hitomi2500/wasca/fpga_firmware_lattice_module/hdl/top.v

`include "timescale.v"

module top(
    input wire clk_25,
    output wire [5:0] led,
    inout wire sd_cmd,
	inout wire [3:0] sd_dat,
	output wire sd_clk,
    output wire uart_tx,
    input wire uart_rx,
	//A-bus slave interface
	input wire [24:1] abus_address,
	inout wire [15:0] abus_data,
	input wire [2:0] abus_chipselect,
	input wire abus_read,
	input wire [1:0] abus_write,
	output wire abus_interrupt,
	output wire abus_direction,
	output wire abus_interrupt_disable_out,
	output wire abus_buffers_enable,
	//SDRAM port 1 (built into icesugar) master interface
	output wire [12:0] sdram_addr,
	output wire [1:0] sdram_ba,
	output wire sdram_cas_n,
	output wire sdram_cke,
	output wire sdram_cs_n,
	inout wire [15:0] sdram_dq,
	output wire [1:0] sdram_dqm,
	output wire sdram_ras_n,
	output wire sdram_we_n,
	output wire sdram_clk,
	//SDRAM port 2 (external on wasca board) master interface
	output wire [12:0] sdram2_addr,
	output wire [1:0] sdram2_ba,
	output wire sdram2_cas_n,
	output wire sdram2_cke,
	output wire sdram2_cs_n,
	inout wire [7:0] sdram2_dq,
	output wire [1:0] sdram2_dqm,
	output wire sdram2_ras_n,
	output wire sdram2_we_n,
	output wire sdram2_clk,
    //qspi port, unused
    input wire qspi_cs,
    input wire [3:0] qspi_d,
    //i2c
    input wire scsp_clk,
    output wire ssel,
    output wire i2s_bclk,
    output wire i2s_lrclk,
    output wire i2s_dout,
	//debug
	output wire debug_1,
	output wire debug_2,
	output wire debug_3,
	output wire debug_4
);

wire clk_50;
wire clk_133;
wire sd_clk_internal;
wire [3:0] sdram_debug;
wire [0:0] sdram2_dqm_lo;
wire i2s_bclk_internal;
wire i2s_lrclk_internal;
wire i2s_dout_internal;
wire i2s_ssel_internal;
wire i2s_test_enable;

pll_25_133 pll(
    .clk_in_25(clk_25),
    .clk_out_50(clk_50),
    .clk_out_133(clk_133)
);

attosoc soc(
    .mcu_clk_i(clk_50),
    .sdram_clk_i(clk_133),
    .led(led),
    .sd_clk_i(clk_25),
    .sd_cmd(sd_cmd),
    .sd_dat(sd_dat),
    .sd_clk(sd_clk_internal),
    .uart_tx(uart_tx),
    .uart_rx(uart_rx),
    //A-bus slave interface
    .abus_address(abus_address),
    .abus_data(abus_data),
    .abus_chipselect(abus_chipselect),
    .abus_read(abus_read),
    .abus_write(abus_write),
    .abus_interrupt(abus_interrupt),
    .abus_direction(abus_direction),
    .abus_interrupt_disable_out(abus_interrupt_disable_out),
    //SDRAM port 1 (built into icesugar) master interface
    .sdram_addr(sdram_addr),
    .sdram_ba(sdram_ba),
    .sdram_cas_n(sdram_cas_n),
    .sdram_cke(sdram_cke),
    .sdram_cs_n(sdram_cs_n),
    .sdram_dq(sdram_dq),
    .sdram_dqm(sdram_dqm),
    .sdram_ras_n(sdram_ras_n),
    .sdram_we_n(sdram_we_n),
    .sdram_clk(sdram_clk),
    //SDRAM port 2 (external on wasca board) master interface
    .sdram2_addr(sdram2_addr),
    .sdram2_ba(sdram2_ba),
    .sdram2_cas_n(sdram2_cas_n),
    .sdram2_cke(sdram2_cke),
    .sdram2_cs_n(sdram2_cs_n),
    .sdram2_dq(sdram2_dq),
    .sdram2_dqm(sdram2_dqm_lo),
    .sdram2_ras_n(sdram2_ras_n),
    .sdram2_we_n(sdram2_we_n),
    .sdram2_clk(sdram2_clk),
    .sdram_debug(sdram_debug)
);

/*i2s_test_core test_gen(
    .clk(scsp_clk),
    .bck(i2s_bclk_internal),
    .ws(i2s_lrclk_internal),
    .data(i2s_dout_internal),
    .ssel(i2s_ssel_internal)
);*/

assign i2s_test_enable = 0;//sdram_debug[0];

assign ssel = (i2s_test_enable) ? i2s_ssel_internal : 1'b1;//1'b1;//I2S override, should be 1 if not using I2S
assign i2s_bclk = (i2s_test_enable) ? i2s_bclk_internal : 0;
assign i2s_lrclk = (i2s_test_enable) ? i2s_lrclk_internal : 0;
assign i2s_dout = (i2s_test_enable) ? i2s_dout_internal : 0;

assign sd_clk = sd_clk_internal;
assign abus_buffers_enable = 0;//1'b1;
assign sdram2_dqm = {sdram2_dqm_lo[0],sdram2_dqm_lo[0]};
assign debug_1 = 0;//scsp_clk;//abus_address[0];//sdram_debug[0];
assign debug_2 = 0;//i2s_bclk_internal;//abus_address[1];//sdram_debug[1];
assign debug_3 = 0;//i2s_lrclk_internal;//abus_address[2];//sdram_debug[2];
assign debug_4 = 0;//i2s_dout_internal;//abus_address[3];//sdram_debug[3];

endmodule
