hitomi2500/wasca/fpga_firmware_lattice_module/picorv_firmware/firmware.c

#include <stdlib.h>
#include <string.h>
#include <stdint.h>
#include "fatfs/ff.h"
#include "fatfs/sdiodrv.h"
#include "fatfs/diskio.h"
#include "mini-printf.h"

#define VERSION_MAJOR 2
#define VERSION_MINOR 1

#define WISHBONE_REG_PCNTR 0x0
#define WISHBONE_REG_FSCNTRL 0x1
#define WISHBONE_REG_MODE 0x2
#define WISHBONE_REG_HWVER 0x3
#define WISHBONE_REG_SWVER 0x4
#define WISHBONE_REG_SNIFFER_DATA 0x5
#define WISHBONE_REG_SNIFFER_CONTROL 0x8
#define WISHBONE_REG_MAPPER_READ_LO 0x9
#define WISHBONE_REG_MAPPER_READ_HI 0xa
#define WISHBONE_REG_MAPPER_WRITE_LO 0xb
#define WISHBONE_REG_MAPPER_WRITE_HI 0xc
#define WISHBONE_REG_COUNTER_RESET 0xd
#define WISHBONE_REG_RAM_1M_ALIASING 0xe
#define WISHBONE_REG_ID 0xf

#define LED_OFF 0x0
#define LED_EXT_RED 0x20
#define LED_EXT_GREEN 0x10
#define LED_EXT_BLUE 0x8
#define LED_EXT_CYAN (LED_EXT_GREEN | LED_EXT_BLUE)
#define LED_EXT_MAGENTA (LED_EXT_RED | LED_EXT_BLUE)
#define LED_EXT_YELLOW (LED_EXT_RED | LED_EXT_GREEN)
#define LED_EXT_WHITE (LED_EXT_RED | LED_EXT_GREEN | LED_EXT_BLUE)

unsigned char buffer[2048];

#define LED (*(volatile uint32_t*)0x02000000)

#define reg_uart_clkdiv (*(volatile uint32_t*)0x02000004)
//#define reg_uart_data (*(volatile uint32_t*)0x02000008)

#define BLKSIZE 512
#define BLKCNT 10

char roms_filenames[32][64];

__attribute__((aligned(4))) PARTITION VolToPart[FF_VOLUMES] = {
    {0, 0},   // logical drive 0: physical drive 0, auto-detect
};

volatile uint32_t * pWishboneRegs = (uint32_t *)0x01000000;
volatile uint32_t * pSDRAM = (uint32_t *)0x10000000;
volatile uint32_t * pSDRAM2 = (uint32_t *)0x14000000;

__attribute__((aligned(4))) FATFS FatFs;		/* FatFs work area needed for each volume */

int overall_backup_enable = 0;
int overall_backup_counter = 0;

extern void filesystem_access_init();
extern void filesystem_access_scheduler();

void delay() {
    //for (volatile int i = 0; i < 2500000; i++)
    for (volatile int i = 0; i < 750000; i++)
    //for (volatile int i = 0; i < 250; i++)
        ;
}

uint32_t lsfr_next_random (uint32_t prev)
{
	if ( ((prev&0x80000000)/0x80000000)^((prev&0x40000000)/0x40000000)^((prev&0x10)/0x10)^((prev&0x8)/0x8) )
		return  (prev & 0x7FFFFFFF)* 2 + 1;
	else 
		return  (prev & 0x7FFFFFFF)* 2;
}

char* mini_strcpy(char* dest, const char* src) {
    int i = 0;
    while (src[i] != '\0') {
        dest[i] = src[i];
        i++;
    }
    dest[i] = '\0'; // Properly terminate the string
    return dest;
}

char* mini_strcat(char* dest, const char* src) {
    char* ptr = dest;
    while (*ptr != '\0') ptr++; // Find end of dest
    while ((*ptr++ = *src++) != '\0'); // Copy src to dest
    return dest;
}

char* mini_strstr(const char *haystack, const char *needle) {
    // If needle is empty, return the entire haystack
    if (*needle == '\0') return (char *)haystack;

    for (; *haystack != '\0'; haystack++) {
        // If first character matches, check the rest
        if (*haystack == *needle) {
            const char *h = haystack;
            const char *n = needle;
            
            // Compare characters
            while (*h != '\0' && *n != '\0' && *h == *n) {
                h++;
                n++;
            }
            // If we reached the end of the needle, it's a match
            if (*n == '\0') return (char *)haystack;
        }
    }
    return NULL; // Needle not found
}

int sdram_quicktest() {
	volatile uint32_t a;
	int errors = 0;
	uint32_t backup[64];
	//CS0
	backup[0] = pSDRAM[0];
	for (int i=0;i<24;i++)
		backup[i+1] = pSDRAM[1<<i];
	backup[31] = pSDRAM[0xffffff];
	pSDRAM[0] = 0x12345678;
	for (int i=0;i<24;i++)
		pSDRAM[1<<i] = 0x11111111*i;
	pSDRAM[0xffffff] = 0xdeafface;
	a = pSDRAM[0];
	if (a != 0x00005678) {
		mini_printf("SDRAM QUICK error: addr %x write %x read %x\r\n",0,0x00005678,a);
		errors++;
	}
	for (int i=0;i<24;i++) {
		a = pSDRAM[1<<i];
		if (a !=((0x1111*i) & 0xFFFF)) {
			mini_printf("SDRAM QUICK error: addr %x write %x read %x\r\n",1<<i,((0x1111*i) & 0xFFFF),a);
			errors++;
		}
	}
	a = pSDRAM[0xffffff];
	if (a != 0x0000face) {
		mini_printf("SDRAM QUICK error: addr %x write %x read %x\r\n",0xffffff,0x0000face,a);
		errors++;
	}
	pSDRAM[0] = backup[0];
	for (int i=0;i<24;i++)
		pSDRAM[1<<i] = backup[i+1];
	pSDRAM[0xffffff] = backup[31];
	//CS1
	backup[0] = pSDRAM2[0];
	for (int i=0;i<24;i++)
		backup[i+1] = pSDRAM2[1<<i];
	backup[31] = pSDRAM2[0xffffff];
	pSDRAM2[0] = 0x6789;
	for (int i=0;i<23;i++)
		pSDRAM2[1<<i] = 0x1020*i;
	pSDRAM2[0x7fffff] = 0xdeadbeef;
	a = pSDRAM2[0];
	if (a != 0x6789) {
		mini_printf("SDRAM2 QUICK error: addr %x write %x read %x\r\n",0,0x6789,a);
		errors++;
	}
	for (int i=0;i<23;i++) {
		a = pSDRAM2[1<<i];
		if (a !=((0x1020*i) & 0xFFFF)) {
			mini_printf("SDRAM2 QUICK error: addr %x write %x read %x\r\n",1<<i,((0x1020*i) & 0xFFFF),a);
			errors++;
		}
	}
	a = pSDRAM2[0x7fffff];
	if (a != 0xbeef) {
		mini_printf("SDRAM2 QUICK error: addr %x write %x read %x\r\n",0x7fffff,0xbeef,a);
		errors++;
	}
	pSDRAM2[0] = backup[0];
	for (int i=0;i<24;i++)
		pSDRAM2[1<<i] = backup[i+1];
	pSDRAM2[0xffffff] = backup[31];	
	return errors;
}

void backup_sync_sector(int sector, FIL * _file) {
	int written = 0;
	uint16_t * buffer16 = (uint16_t *)buffer;
	//sync data
	for (int i=0;i<256;i++)
		buffer16[i] = pSDRAM2[sector*256+i];
	f_lseek(_file,sector*512);
	int result = f_write(_file,buffer,512,&written);
	if (result)
		mini_printf("Sync error at %d, written %d result %d\r\n",sector,written,result);
	result = f_sync(_file);
	if (result)
		mini_printf("Sync error2 at %d, written %d result %d\r\n",sector,written,result);
}

void sniffer_purge_fifo () {
	volatile int dummy;
	while ((pWishboneRegs[WISHBONE_REG_SNIFFER_CONTROL]>>16) > 100) //purging fifo
		dummy = pWishboneRegs[WISHBONE_REG_SNIFFER_DATA];
}

void prepare_advertisement (int roms_count) {
	FILINFO _filinfo;
	//preparing advertisement lines for modes at the middle of CS0
	volatile uint32_t * pAdvertise = (uint32_t *)0x12000000;
	char adv_string[64];
	uint16_t * adv_string16 = (uint16_t*)adv_string;
	int adv_offset = 0;
	int id = 1;
	//power memory 0.5
	pAdvertise[adv_offset] = (id++)<<8;
	memset(adv_string,0,64);
	if (FR_OK == f_stat("backup05.bin", &_filinfo))
		mini_strcpy(adv_string,"BACKUP 0.5M (backup05.bin)");
	else
		mini_strcpy(adv_string,"BACKUP 0.5M (New file: backup05.bin)");
	for (int i=0; i<31;i++)
		pAdvertise[adv_offset+i+1] = adv_string16[i];
	adv_offset+= 32;
	//power memory 1
	memset(adv_string,0,64);
	pAdvertise[adv_offset] = (id++)<<8;
	if (FR_OK == f_stat("backup1.bin", &_filinfo))
		mini_strcpy(adv_string,"BACKUP 1M (backup1.bin)");
	else
		mini_strcpy(adv_string,"BACKUP 1M (New file: backup1.bin)");
	for (int i=0; i<31;i++)
		pAdvertise[adv_offset+i+1] = adv_string16[i];
	adv_offset+= 32;
	//power memory 2
	memset(adv_string,0,64);
	pAdvertise[adv_offset] = (id++)<<8;
	if (FR_OK == f_stat("backup2.bin", &_filinfo))
		mini_strcpy(adv_string,"BACKUP 2M (backup2.bin)");
	else
		mini_strcpy(adv_string,"BACKUP 2M (New file: backup2.bin)");
	for (int i=0; i<31;i++)
		pAdvertise[adv_offset+i+1] = adv_string16[i];
	adv_offset+= 32;
	//power memory 4
	memset(adv_string,0,64);
	pAdvertise[adv_offset] = (id++)<<8;
	if (FR_OK == f_stat("backup4.bin", &_filinfo))
		mini_strcpy(adv_string,"BACKUP 4M (backup4.bin)");
	else
		mini_strcpy(adv_string,"BACKUP 4M (New file: backup4.bin)");
	for (int i=0; i<31;i++)
		pAdvertise[adv_offset+i+1] = adv_string16[i];
	adv_offset+= 32;
	//1M RAM
	memset(adv_string,0,64);
	pAdvertise[adv_offset] = (id++)<<8;
	mini_strcpy(adv_string,"RAM 1M");
	for (int i=0; i<31;i++)
		pAdvertise[adv_offset+i+1] = adv_string16[i];
	adv_offset+= 32;
	//4M RAM
	memset(adv_string,0,64);
	pAdvertise[adv_offset] = (id++)<<8;
	mini_strcpy(adv_string,"RAM 4M");
	for (int i=0; i<31;i++)
		pAdvertise[adv_offset+i+1] = adv_string16[i];
	adv_offset+= 32;
	//special Heart of Darkness mode
	memset(adv_string,0,64);
	pAdvertise[adv_offset] = (id++)<<8;
	mini_strcpy(adv_string,"RAM (Heart of Darkness)");
	for (int i=0; i<31;i++)
		pAdvertise[adv_offset+i+1] = adv_string16[i];
	adv_offset+= 32;
	//now listing rom files
	for (int i=0;i<roms_count;i++){
		memset(adv_string,0,64);
		pAdvertise[adv_offset] = (id++)<<8;
		mini_strcpy(adv_string,"ROM (");
		mini_strcat(adv_string,roms_filenames[i]);
		mini_strcat(adv_string,")");
		for (int i=0; i<31;i++)
			pAdvertise[adv_offset+i+1] = adv_string16[i];
		adv_offset+= 32;
	}
	pAdvertise[adv_offset] = 0;//end of advertising list
}

void report_readiness (int percent) {
	pWishboneRegs[WISHBONE_REG_PCNTR] = percent;
}

void prepare_mode () {
	FILINFO _filinfo;
	int creating_backup = 0;
	FIL _file;
	unsigned int readen;
	uint16_t * buffer16 = (uint16_t *)buffer;
	int offset;
	//executing prepare sequence
	switch (pWishboneRegs[WISHBONE_REG_MODE]) {
		case 0:
			//some error? we never advertised 0
			pWishboneRegs[WISHBONE_REG_ID] = 0xFFFF;
			report_readiness(100);
			LED = LED_EXT_RED;
			break;
		case 1:
			pWishboneRegs[WISHBONE_REG_ID] = 0xFF21;
			if (FR_OK != f_stat("backup05.bin", &_filinfo))
			{
				creating_backup = 1;
				f_open(&_file,"backup05.bin",FA_CREATE_ALWAYS | FA_WRITE);
				for (int i=0;i<1024*2;i++) {
					backup_sync_sector(i,&_file);
					report_readiness((i * 50)/(1024*2));
					LED = (i&0x40) ? LED_EXT_MAGENTA : LED_OFF;
				}
				f_close(&_file);
			}
			f_open(&_file,"backup05.bin",FA_READ);
			f_lseek(&_file,0);
			for (int i=0;i<1024;i++) {
				f_read(&_file,buffer,1024,&readen);
				for (int j=0;j<512;j++) {
					pSDRAM2[i*512+j] = buffer16[j];
				}
				report_readiness( (creating_backup) ? 50 + (i*50)/1024 : (i*100)/1024 );
				LED = (i&0x20) ? LED_EXT_YELLOW : LED_OFF;
			}
			f_close(&_file);
			//keep file open
			report_readiness(100);
			pWishboneRegs[WISHBONE_REG_MAPPER_READ_LO] = 0xFFFFFFFF;//allow full CS0 RAM in backup more
			pWishboneRegs[WISHBONE_REG_MAPPER_WRITE_LO] = 0xFFFFFFFF;//allow full CS0 RAM in backup more
			pWishboneRegs[WISHBONE_REG_MAPPER_WRITE_HI] = 0x0000FFFF;//enable write for CS1
			LED = LED_EXT_GREEN;
			break;
		case 2:
			pWishboneRegs[WISHBONE_REG_ID] = 0xFF22;
			report_readiness(1);
			if (FR_OK != f_stat("backup1.bin", &_filinfo))
			{
				creating_backup = 1;
				f_open(&_file,"backup1.bin",FA_CREATE_ALWAYS | FA_WRITE);
				for (int i=0;i<2048*2;i++) {
					backup_sync_sector(i,&_file);
					report_readiness( (i * 50)/(2048*2) );
					LED = (i&0x40) ? LED_EXT_MAGENTA : LED_OFF;
				}
				f_close(&_file);
			}
			f_open(&_file,"backup1.bin",FA_READ);
			offset = 0;
			while(false == f_eof(&_file)) {
				readen = -1;
				f_read(&_file,buffer,1024,&readen);
				for (int i=0;i<512;i++) {
					pSDRAM2[offset+i] = buffer16[i];
				}
				offset+=512;
				report_readiness( (creating_backup) ? 50 + offset/20972 : offset/10486 );
				LED = (offset&0x4000) ? LED_EXT_YELLOW : LED_OFF;
			}
			f_close(&_file);
			//keep file open
			report_readiness(100);
			pWishboneRegs[WISHBONE_REG_MAPPER_READ_LO] = 0xFFFFFFFF;//allow full CS0 RAM in backup more
			pWishboneRegs[WISHBONE_REG_MAPPER_WRITE_LO] = 0xFFFFFFFF;//allow full CS0 RAM in backup more
			pWishboneRegs[WISHBONE_REG_MAPPER_WRITE_HI] = 0x0000FFFF;//enable write for CS1
			LED = LED_EXT_GREEN;
			break;
		case 3:
			pWishboneRegs[WISHBONE_REG_ID] = 0xFF23;
			report_readiness(1);
			if (FR_OK != f_stat("backup2.bin", &_filinfo))
			{
				creating_backup = 1;
				f_open(&_file,"backup2.bin",FA_CREATE_ALWAYS | FA_WRITE);
				for (int i=0;i<4096*2;i++) {
					backup_sync_sector(i,&_file);
					report_readiness( (i * 50)/(4096*2) );
					LED = (i&0x40) ? LED_EXT_MAGENTA : LED_OFF;
				}
				f_close(&_file);
			}
			f_open(&_file,"backup2.bin",FA_READ);
			offset = 0;
			while(false == f_eof(&_file)) {
				readen = -1;
				f_read(&_file,buffer,1024,&readen);
				for (int i=0;i<512;i++) {
					pSDRAM2[offset+i] = buffer16[i];
				}
				offset+=512;
				report_readiness( (creating_backup) ? 50 + offset/41943 : offset/20972 );
				LED = (offset&0x4000) ? LED_EXT_YELLOW : LED_OFF;
			}
			f_close(&_file);
			//keep file open
			report_readiness(100);
			pWishboneRegs[WISHBONE_REG_MAPPER_READ_LO] = 0xFFFFFFFF;//allow full CS0 RAM in backup more
			pWishboneRegs[WISHBONE_REG_MAPPER_WRITE_LO] = 0xFFFFFFFF;//allow full CS0 RAM in backup more
			pWishboneRegs[WISHBONE_REG_MAPPER_WRITE_HI] = 0x0000FFFF;//enable write for CS1
			LED = LED_EXT_GREEN;
			break;
		case 4:
			pWishboneRegs[WISHBONE_REG_ID] = 0xFF24;
			report_readiness(1);
			if (FR_OK != f_stat("backup4.bin", &_filinfo))
			{
				creating_backup = 1;
				f_open(&_file,"backup4.bin",FA_CREATE_ALWAYS | FA_WRITE);
				for (int i=0;i<8192*2;i++) {
					backup_sync_sector(i,&_file);
					report_readiness( (i * 50)/(8192*2) );
					LED = (i&0x40) ? LED_EXT_MAGENTA : LED_OFF;
				}
				f_close(&_file);
			}
			f_open(&_file,"backup4.bin",FA_READ);
			offset = 0;
			while(false == f_eof(&_file)) {
				readen = -1;
				f_read(&_file,buffer,1024,&readen);
				for (int i=0;i<512;i++) {
					pSDRAM2[offset+i] = buffer16[i];
				}
				offset+=512;
				report_readiness( (creating_backup) ? 50 + offset/83886 : offset/41943 );
				LED = (offset&0x4000) ? LED_EXT_YELLOW : LED_OFF;
			}
			f_close(&_file);
			//keep file open
			report_readiness(100);
			pWishboneRegs[WISHBONE_REG_MAPPER_READ_LO] = 0xFFFFFFFF;//allow full CS0 RAM in backup more
			pWishboneRegs[WISHBONE_REG_MAPPER_WRITE_LO] = 0xFFFFFFFF;//allow full CS0 RAM in backup more
			pWishboneRegs[WISHBONE_REG_MAPPER_WRITE_HI] = 0x0000FFFF;//enable write for CS1
			LED = LED_EXT_GREEN;
			break;
		case 5:
			pWishboneRegs[WISHBONE_REG_RAM_1M_ALIASING] = 0x1;
			pWishboneRegs[WISHBONE_REG_ID] = 0xFF5A;
			report_readiness(100);
			pWishboneRegs[WISHBONE_REG_MAPPER_WRITE_LO] = 0xFFFFFFFF;//enable write for CS0
			pWishboneRegs[WISHBONE_REG_MAPPER_READ_HI] = 0x00008000;//disable read for CS1
			LED = LED_EXT_GREEN;
			break;
		case 6:
			pWishboneRegs[WISHBONE_REG_ID] = 0xFF5C;
			report_readiness(100);
			pWishboneRegs[WISHBONE_REG_MAPPER_WRITE_LO] = 0xFFFFFFFF;//enable write for CS0
			pWishboneRegs[WISHBONE_REG_MAPPER_READ_HI] = 0x00008000;//disable read for CS1
			LED = LED_EXT_GREEN;
			break;
		case 7:
			pWishboneRegs[WISHBONE_REG_ID] = 0x1234;
			report_readiness(100);
			pWishboneRegs[WISHBONE_REG_MAPPER_READ_LO] = 0x80000000;//disable read for CS0
			pWishboneRegs[WISHBONE_REG_MAPPER_WRITE_HI] = 0x0000FFFF;//enable write for CS1
			LED = LED_EXT_GREEN;
			break;
		default:
			pWishboneRegs[WISHBONE_REG_ID] = 0xFFFF;
			//getting rom
			f_open(&_file,roms_filenames[pWishboneRegs[WISHBONE_REG_MODE]-8],FA_READ);
			int _size = f_size(&_file);
			offset = 0;
			while(false == f_eof(&_file)) {
				readen = -1;
				f_read(&_file,buffer,1024,&readen);
				for (int i=0;i<512;i++) {
					pSDRAM[offset+i] = buffer16[i];
				}
				offset+=512;
				report_readiness( (200*offset)/_size );
				LED = (offset&0x4000) ? LED_EXT_YELLOW : LED_OFF;
			}
			f_close(&_file);
			report_readiness(100);
			pWishboneRegs[WISHBONE_REG_MAPPER_WRITE_LO] = 0xFFFFFFFF;//enable write for CS0
			pWishboneRegs[WISHBONE_REG_MAPPER_WRITE_HI] = 0x0000FFFF;//enable write for CS1
			LED = LED_EXT_GREEN;
			break;
	}

	delay();
	LED = LED_OFF;

	//setup sniffer
	switch (pWishboneRegs[WISHBONE_REG_MODE]) {
		case 0:
			pWishboneRegs[WISHBONE_REG_SNIFFER_CONTROL] = 0x0;//broken config, not sniffing anything
			break;
		case 1:
		case 2:
		case 3:
		case 4:
			pWishboneRegs[WISHBONE_REG_SNIFFER_CONTROL] = 0xA;//sniffing only writes over CS1
			break;
		case 5:
		case 6:
			pWishboneRegs[WISHBONE_REG_SNIFFER_CONTROL] = 0x6;//sniffing only writes over CS0
			break;
		case 7:
			pWishboneRegs[WISHBONE_REG_SNIFFER_CONTROL] = 0xA;//sniffing only writes over CS1
			break;
		default:
			pWishboneRegs[WISHBONE_REG_SNIFFER_CONTROL] = 0xF;//sniffing all access over CS0 and CS1
			break;
    }

	//remove bootable signature for everything except roms
	switch (pWishboneRegs[WISHBONE_REG_MODE]) {
		case 1:
		case 2:
		case 3:
		case 4:
		case 5:
		case 6:
		case 7:
			for (int i=0;i<256;i++)
				pSDRAM[i]  = 0;
			break;
		default:
			break;
    }
}

void sync_mode () {
	FIL _file;
	volatile int dummy;
	switch (pWishboneRegs[WISHBONE_REG_MODE]) {
		case 1:
			//backup syncing + led blinking
			if (pWishboneRegs[WISHBONE_REG_SNIFFER_CONTROL] & 0x07FF0000) {
				if ( (pWishboneRegs[WISHBONE_REG_SNIFFER_CONTROL]>>16) > 1000) { //fifo overfill, error
					LED = LED_EXT_RED;
					while (1);
				}
				if ( (pWishboneRegs[WISHBONE_REG_SNIFFER_CONTROL]>>16) > 512) { //fifo half-full, switching to overall mode 
					overall_backup_enable = 1;
					overall_backup_counter = 0;
				}
				if (overall_backup_enable) {
					f_open(&_file,"backup05.bin",FA_READ | FA_WRITE);
					LED = (overall_backup_counter & 0x20) ? LED_EXT_CYAN : LED_OFF;
					sniffer_purge_fifo();
					backup_sync_sector(overall_backup_counter,&_file);
					sniffer_purge_fifo();
					overall_backup_counter++;
					if (overall_backup_counter*512 >= 1024*1024) {
						//sync sectors 0 and 1 at the end, because that's what bios does?
						backup_sync_sector(0,&_file);
						backup_sync_sector(1,&_file);
						//stop overall sync mode
						overall_backup_enable = 0;
					}
					f_close(&_file);
				} else {
					LED = LED_EXT_MAGENTA;
					//read fifo
					int sector = pWishboneRegs[WISHBONE_REG_SNIFFER_DATA];
					f_open(&_file,"backup05.bin",FA_READ | FA_WRITE);
					backup_sync_sector(sector,&_file);
					f_close(&_file);
				}
			}
			else
				LED = LED_OFF;
			break;
		case 2:
			//backup syncing + led blinking
			if (pWishboneRegs[WISHBONE_REG_SNIFFER_CONTROL] & 0x07FF0000) {
				if ( (pWishboneRegs[WISHBONE_REG_SNIFFER_CONTROL]>>16) > 1000) { //fifo overfill, error
					LED = LED_EXT_RED;
					while (1);
				}
				if ( (pWishboneRegs[WISHBONE_REG_SNIFFER_CONTROL]>>16) > 512) { //fifo half-full, switching to overall mode 
					overall_backup_enable = 1;
					overall_backup_counter = 0;
				}
				if (overall_backup_enable) {
					f_open(&_file,"backup1.bin",FA_READ | FA_WRITE);
					LED = (overall_backup_counter & 0x20) ? LED_EXT_CYAN : LED_OFF;
					sniffer_purge_fifo();
					backup_sync_sector(overall_backup_counter,&_file);
					sniffer_purge_fifo();
					overall_backup_counter++;
					if (overall_backup_counter*512 >= 2048*1024) {
						//sync sectors 0 and 1 at the end, because that's what bios does?
						backup_sync_sector(0,&_file);
						backup_sync_sector(1,&_file);
						//stop overall sync mode
						overall_backup_enable = 0;
					}
					f_close(&_file);
				} else {
					LED = LED_EXT_MAGENTA;
					//read fifo
					int sector = pWishboneRegs[WISHBONE_REG_SNIFFER_DATA];
					f_open(&_file,"backup1.bin",FA_READ | FA_WRITE);
					backup_sync_sector(sector,&_file);
					f_close(&_file);
				}
			}
			else
				LED = LED_OFF;
			break;
		case 3:
			//backup syncing + led blinking
			if (pWishboneRegs[WISHBONE_REG_SNIFFER_CONTROL] & 0x07FF0000) {
				if ( (pWishboneRegs[WISHBONE_REG_SNIFFER_CONTROL]>>16) > 1000) { //fifo overfill, error
					LED = LED_EXT_RED;
					while (1);
				}
				if ( (pWishboneRegs[WISHBONE_REG_SNIFFER_CONTROL]>>16) > 512) { //fifo half-full, switching to overall mode 
					overall_backup_enable = 1;
					overall_backup_counter = 0;
				}
				if (overall_backup_enable) {
					f_open(&_file,"backup2.bin",FA_READ | FA_WRITE);
					LED = (overall_backup_counter & 0x20) ? LED_EXT_CYAN : LED_OFF;
					sniffer_purge_fifo();
					backup_sync_sector(overall_backup_counter,&_file);
					sniffer_purge_fifo();
					overall_backup_counter++;
					if (overall_backup_counter*512 >= 4096*1024) {
						//sync sectors 0 and 1 at the end, because that's what bios does?
						backup_sync_sector(0,&_file);
						backup_sync_sector(1,&_file);
						//stop overall sync mode
						overall_backup_enable = 0;
					}
					f_close(&_file);
				} else {
					LED = LED_EXT_MAGENTA;
					//read fifo
					int sector = pWishboneRegs[WISHBONE_REG_SNIFFER_DATA];
					f_open(&_file,"backup2.bin",FA_READ | FA_WRITE);
					backup_sync_sector(sector,&_file);
					f_close(&_file);
				}
			}
			else
				LED = LED_OFF;
			break;
		case 4:
			//backup syncing + led blinking
			if (pWishboneRegs[WISHBONE_REG_SNIFFER_CONTROL] & 0x07FF0000) {
				if ( (pWishboneRegs[WISHBONE_REG_SNIFFER_CONTROL]>>16) > 1000) { //fifo overfill, error
					LED = LED_EXT_RED;
					while (1);
				}
				if ( (pWishboneRegs[WISHBONE_REG_SNIFFER_CONTROL]>>16) > 512) { //fifo half-full, switching to overall mode 
					overall_backup_enable = 1;
					overall_backup_counter = 0;
				}
				if (overall_backup_enable) {
					f_open(&_file,"backup4.bin",FA_READ | FA_WRITE);
					LED = (overall_backup_counter & 0x20) ? LED_EXT_CYAN : LED_OFF;
					sniffer_purge_fifo();
					backup_sync_sector(overall_backup_counter,&_file);
					sniffer_purge_fifo();
					overall_backup_counter++;
					if (overall_backup_counter*512 >= 8192*1024) {
						//sync sectors 0 and 1 at the end, because that's what bios does?
						backup_sync_sector(0,&_file);
						backup_sync_sector(1,&_file);
						//stop overall sync mode
						overall_backup_enable = 0;
					}
					f_close(&_file);
				} else {
					LED = LED_EXT_MAGENTA;
					//read fifo
					int sector = pWishboneRegs[WISHBONE_REG_SNIFFER_DATA];
					f_open(&_file,"backup4.bin",FA_READ | FA_WRITE);
					backup_sync_sector(sector,&_file);
					f_close(&_file);
				}
			}
			else
				LED = LED_OFF;
			break;
		case 5:
		case 6:
			//led blinking only
			if (pWishboneRegs[WISHBONE_REG_SNIFFER_CONTROL] & 0x07FF0000) {
				//read fifo
				dummy = pWishboneRegs[WISHBONE_REG_SNIFFER_DATA];
				LED = LED_EXT_GREEN;
			}
			else
				LED = LED_OFF;
			break;
		case 7:
			//led blinking only
			if (pWishboneRegs[WISHBONE_REG_SNIFFER_CONTROL] & 0x07FF0000) {
				//read fifo
				dummy = pWishboneRegs[WISHBONE_REG_SNIFFER_DATA];
				LED = LED_EXT_GREEN;
			}
			else
				LED = LED_OFF;
			break;
		default:
			//led blinking only
			/*if (pWishboneRegs[WISHBONE_REG_SNIFFER_CONTROL] & 0x07FF0000) {
				//read fifo
				dummy = pWishboneRegs[WISHBONE_REG_SNIFFER_DATA];
				LED = LED_EXT_GREEN;
			}
			else
				LED = LED_OFF;*/
			break;  
		}
}

int main() {
	LED = LED_EXT_RED; //start with red led
	//not setting uart, done in bootstrap

	uint16_t * buffer16 = (uint16_t *)buffer;
	volatile int dummy;

	//set version
	pWishboneRegs[WISHBONE_REG_SWVER] = 0x0101; //software version register
	
	//set wishbone registers
	pWishboneRegs[WISHBONE_REG_SNIFFER_CONTROL] = 0xA;//sniffing only writes over CS1
	pWishboneRegs[WISHBONE_REG_MAPPER_READ_LO] = 0xFFFFFFFF;//read mapper for CS0
	pWishboneRegs[WISHBONE_REG_MAPPER_READ_HI] = 0x0000FFFF;//read mapper for CS1 + CS2
	pWishboneRegs[WISHBONE_REG_MAPPER_WRITE_LO] = 0xFFFFFFFF;//write mapper for CS0
	pWishboneRegs[WISHBONE_REG_MAPPER_WRITE_HI] = 0x0000FFFF;//0x00000000;//write mapper for CS1 + CS2

	//set memory-based registers
	pSDRAM[0xfffd00] =  0; //filesystem status register
	pSDRAM[0xfffffc] =  VERSION_MAJOR | VERSION_MINOR<<8; //Software version
	pSDRAM[0xfffffd] =  0x6177; //signature "wa"
	pSDRAM[0xfffffe] =  0x6373; //signature "sc"
	pSDRAM[0xffffff] =  0x2061; //signature "a "

	//not writing fallback rom, done in bootstrap
	
	mini_printf("wasca firmware %s %s\r\n",__DATE__,__TIME__);

	sdram_quicktest();
	mini_printf("SDRAM test done.\r\n");

	mini_printf("Mount SD...");
	FRESULT fr = f_mount(&FatFs, "0:/", 1);	//mount SD card
	mini_printf("OK\r\n");

	DIR _dir;
	FILINFO _filinfo;
	mini_printf("Open root dir...");
	fr = f_opendir(&_dir, "");
	mini_printf("OK\r\n");


	//not writing wasca.ss, done in bootstrap
	//but setting led if it's present
	if (FR_OK == f_stat("wasca.ss", &_filinfo))
		LED = LED_EXT_BLUE;

	//getting roms list
	int roms_count = 0;
	_filinfo.fname[0] = 1;
	f_readdir(&_dir,NULL);//rewind to start
	while (_filinfo.fname[0] != 0) {
		fr = f_readdir(&_dir,&_filinfo);
		if ( (mini_strstr(_filinfo.fname,".ss")) || (mini_strstr(_filinfo.fname,".bin")) || (mini_strstr(_filinfo.fname,".SS")) || (mini_strstr(_filinfo.fname,".BIN")) ) {
			if ((memcmp(_filinfo.fname,"wasca.ss",8) != 0) && (memcmp(_filinfo.fname,"backup05.bin",12) != 0) && (memcmp(_filinfo.fname,"backup1.bin",11) != 0) &&
			   												   (memcmp(_filinfo.fname,"backup2.bin",11) != 0) && (memcmp(_filinfo.fname,"backup4.bin",11) != 0) ){
				if (roms_count < 11) {
					memset(roms_filenames[roms_count],0,64);
					mini_strcpy(roms_filenames[roms_count],_filinfo.fname);
					roms_count++;
				}
			}
		}
	}

	filesystem_access_init();
	
	//main cycle
    while (1) {
		if (0 == pWishboneRegs[WISHBONE_REG_MODE]) {
			//going into init mode on start or if user selects mode 0
			pWishboneRegs[WISHBONE_REG_MAPPER_READ_LO] = 0xFFFFFFFF;//read mapper for CS0
			pWishboneRegs[WISHBONE_REG_MAPPER_READ_HI] = 0x0000FFFF;//read mapper for CS1 + CS2
			pWishboneRegs[WISHBONE_REG_MAPPER_WRITE_LO] = 0xFFFFFFFF;//write mapper for CS0
			pWishboneRegs[WISHBONE_REG_MAPPER_WRITE_HI] = 0x0000FFFF;//0x00000000;//write mapper for CS1 + CS2
			prepare_advertisement(roms_count);

			//waiting for mode selection
			mini_printf("Waiting for mode selection...");
			while(pWishboneRegs[WISHBONE_REG_MODE] == 0)
				;
			mini_printf("done, mode %d\r\n",pWishboneRegs[WISHBONE_REG_MODE]);
			
			//disable blue led if it was first init
			LED = LED_OFF;

			//prepare chosen mode
			prepare_mode();
		}
		else {
			sync_mode();
		}
		filesystem_access_scheduler();
	}
}
