hitomi2500/wasca/rp2040_firmware/fpga_updater/spi.c

#include "pico/stdlib.h"

// Replace these macros with your GPIO writes/reads
#include "pins.h"

#define CS_LOW()     gpio_put(QSPI_CS_PIN,0)
#define CS_HIGH()    gpio_put(QSPI_CS_PIN,1)
#define CLK_LOW()    gpio_put(QSPI_CLK_PIN,0)
#define CLK_HIGH()   gpio_put(QSPI_CLK_PIN,1)
#define MOSI_LOW()   gpio_put(QSPI_D0_PIN,0)
#define MOSI_HIGH()  gpio_put(QSPI_D0_PIN,1)
#define MISO_READ()  gpio_get(QSPI_D1_PIN)

static void spi_delay(void) {
    // small delay, or NOPs
    volatile int i=0;
    for (i=0;i<10;i++)
        asm ("nop");
}

static uint8_t spi_txrx(uint8_t v) {
    uint8_t r = 0;

    for (int i = 0; i < 8; i++) {
        CLK_LOW();

        if (v & 0x80) MOSI_HIGH();
        else          MOSI_LOW();

        spi_delay();

        CLK_HIGH();
        r <<= 1;
        if (MISO_READ()) r |= 1;

        spi_delay();
        v <<= 1;
    }

    CLK_LOW();
    return r;
}

static void w25q_write_enable(void) {
    CS_LOW();
    spi_txrx(0x06);          // Write Enable
    CS_HIGH();
    spi_delay();
}

static void w25q_write_disable(void) {
    CS_LOW();
    spi_txrx(0x04);          // Write Disable
    CS_HIGH();
    spi_delay();
}

static uint8_t w25q_read_status1(void) {
    uint8_t s;

    CS_LOW();
    spi_txrx(0x05);          // Read Status Register-1
    s = spi_txrx(0xFF);
    CS_HIGH();
    spi_delay();

    return s;
}

static void w25q_wait_busy(void) {
    while (w25q_read_status1() & 0x01) {
        // WIP/BUSY bit
        spi_delay();
    }
}

void w25q_page_program(uint32_t addr, const uint8_t *data, uint16_t len) {
    if (len > 256) len = 256;

    // Do not cross page boundary
    uint16_t page_remain = 256 - (addr & 0xFF);
    if (len > page_remain) len = page_remain;

    w25q_write_enable();

    CS_LOW();
    spi_txrx(0x02);                  // Page Program
    spi_txrx((addr >> 16) & 0xFF);   // A23..A16
    spi_txrx((addr >> 8) & 0xFF);    // A15..A8
    spi_txrx(addr & 0xFF);           // A7..A0

    for (uint16_t i = 0; i < len; i++) {
        spi_txrx(data[i]);
    }

    CS_HIGH();

    for (int i=0;i<10;i++)
        spi_delay();

    w25q_wait_busy();

    w25q_write_disable();
}

void w25q_sector_erase_4k(uint32_t addr) {
    w25q_write_enable();

    CS_LOW();
    spi_txrx(0x20);                  // Sector Erase 4KB
    spi_txrx((addr >> 16) & 0xFF);
    spi_txrx((addr >> 8) & 0xFF);
    spi_txrx(addr & 0xFF);
    CS_HIGH();

    for (int i=0;i<10;i++)
        spi_delay();

    w25q_wait_busy();

    w25q_write_disable();
}
