hitomi2500/wasca/fpga_firmware_lattice_module/picorv_bootstrap/stdlib_tiny.c

#include <stddef.h>

//typedef union { unsigned int i; float f; } fu;

void * memcpy (void *dest, const void *src, size_t len)
{
  char *d = dest;
  const char *s = src;
  while (len--)
    *d++ = *s++;
  return dest;
}

int memcmp (const void *str1, const void *str2, size_t count)
{
  register const unsigned char *s1 = (const unsigned char*)str1;
  register const unsigned char *s2 = (const unsigned char*)str2;

  while (count-- > 0)
    {
      if (*s1++ != *s2++)
	  return s1[-1] < s2[-1] ? -1 : 1;
    }
  return 0;
}

void * memset (void *dest, int val, size_t len)
{
  unsigned char *ptr = dest;
  while (len-- > 0)
    *ptr++ = val;
  return dest;
}

char * strchr (const char *s, int c)
{
  do {
    if (*s == c)
      {
	return (char*)s;
      }
  } while (*s++);
  return (0);
}

#define CHAR_BIT (8)

int
__clzsi2 (int val)
{
  int i = 32;
  int j = 16;
  int temp;

  for (; j; j >>= 1)
    {
      if (temp = val >> j)
	{
	  if (j == 1)
	    {
	      return (i - 2);
	    }
	  else
	    {
	      i -= j;
	      val = temp;
	    }
	}
    }
  return (i - val);
}
