hitomi2500/wasca/sh2_cart_test/video.h

#ifndef VIDEO_H
#define VIDEO_H

typedef enum {
        VIDEO_SCANMODE_240I = 0,
        VIDEO_SCANMODE_240P = 1,
        VIDEO_SCANMODE_480I = 2,
        VIDEO_SCANMODE_480P = 3
} __packed video_scanmode_t;

typedef enum {
        VIDEO_X_RESOLUTION_320 = 0,
        VIDEO_X_RESOLUTION_352 = 1,
} __packed video_x_resolution_t;

typedef enum {
        BITMAP_MODE_NONE = 0,
        BITMAP_MODE_16_COLORS = 1,
        BITMAP_MODE_256_COLORS = 2,
} __packed bitmap_mode_t;

typedef struct {
        video_scanmode_t scanmode;
        video_x_resolution_t x_res;
        vdp2_tvmd_vert_t y_res;
        bool x_res_doubled;
        vdp2_tvmd_tv_standard_t colorsystem;
} __packed video_screen_mode_t;

void video_init(video_screen_mode_t screen_mode, bitmap_mode_t bmp_mode);
void video_deinit();
int video_is_inited();
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
